uptime-industries/compute-blade/docs/docs/blade/compatibility/switch.md

# Network Switches & PoE Injectors

PoE enabled switch & Injectors which have been used with the Compute Blade

## Cisco
| Product | Model Number | Tested By |
| :--- | :--- | --- |
| Cisco Catalyst 3650 48-FQM | [WS-C3650-48FQM](https://www.cisco.com/c/en/us/products/collateral/switches/catalyst-3650-series-switches/data_sheet-c78-729449.html) | murraythegoz(On Discord) |

## Ubiquiti

| Product | Model Number | Tested By |
| :--- |:--- | --- |
| 8 PoE (Gen1) | [US-8-60W](https://techspecs.ui.com/unifi/switching/us-8-60w) | [einsteinagogo](https://github.com/einsteinagogo) |
| Ultra 60W | [USW-Ultra-60W](https://store.ui.com/us/en/products/usw-ultra-60w) | [dstewart1673](https://github.com/dstewart1673) |
| USW Lite 8 PoE | [USW-LITE-8-POE](https://store.ui.com/us/en/products/usw-lite-8-poe) | [khrystoph](https://github.com/khrystoph) |
| Standard 24 PoE (Gen1) | [US-24-250W](https://techspecs.ui.com/unifi/switching/us-24-250w) | [einsteinagogo](https://github.com/einsteinagogo) |
| Pro 24 PoE | [USW-Pro-24-PoE](https://techspecs.ui.com/unifi/switching/usw-pro-24-poe) | [Uptime](https://github.com/uptime-lab) |
| Pro 48 PoE | [USW-Pro-48-PoE](https://techspecs.ui.com/unifi/switching/usw-pro-48-poe) | [adriano](https://github.com/Adriano8899) |
| PoE+ Adapter (30W) | [U-POE-at](https://techspecs.ui.com/unifi/accessories/u-poe-at) | [mindspore](https://github.com/cKhoff) |
| Pro Max 24 PoE | [USW-Pro-Max-24-PoE](https://techspecs.ui.com/unifi/switching/usw-pro-max-24-poe) | [mindspore](https://github.com/cKhoff) |
| USW Enterprise 8 PoE | [USW-Enterprise-8-PoE (120W)](https://store.ui.com/us/en/category/switching-utility/products/usw-enterprise-8-poe) | [Tom](https://github.com/nyx0) |

## TP-Link

| Product | Model Number | Tested By |
| :--- | :--- | --- |
| TL-SG105MPE | [TL-SG105MPE](https://www.tp-link.com/us/home-networking/5-port-switch/tl-sg105mpe/) | slipstickn(On Discord) |

## Juniper

| Product | Model Number | Tested By |
| :--- |:--- | --- |
| EX2200-48P-4G | [EX2200-48P-4G](https://www.juniper.net/documentation/product/us/en/ex2200/) | [mookie-](https://github.com/mookie-) |

## Brocade

| Product | Model Number | Tested By |
| :--- |:--- | --- |
| ICX 6610 | [ICX 6610-48P](https://webresources.ruckuswireless.com/pdf/datasheets/ds-icx-6610.pdf) | [khrystoph](https://github.com/khrystoph) |

## Mikrotik

| Product | Model Number | Tested By |
| :--- |:--- | --- |
| CRS328-24P-4S+RM | [CRS328-24P-4S+RM](https://mikrotik.com/product/crs328_24p_4s_rm) | [Metrotyranno](https://github.com/metrotyranno) |
| CRS354-48P-4S+2Q+RM | [CRS354-48P-4S+2Q+RM](https://mikrotik.com/product/crs354_48p_4s_2q_rm) | [Metrotyranno](https://github.com/metrotyranno) |
