uptime-industries/compute-blade/docs/docs/bladerunner/19inch/index.mdx

---
sidebar_position: 2
---

# 19 inch Rack

BladeRunner™️ 19-Inch

The Enterprise 19-Inch Enclosure is for deployment at scale. Can be equipped with twenty Compute Blades and ten Fan Units, offering high density compute in a standard 1U of rack space.

Download the [Datasheet](/datasheet/BladeRunner_datasheet_v.1.0.pdf) (PDF)

## Drawing
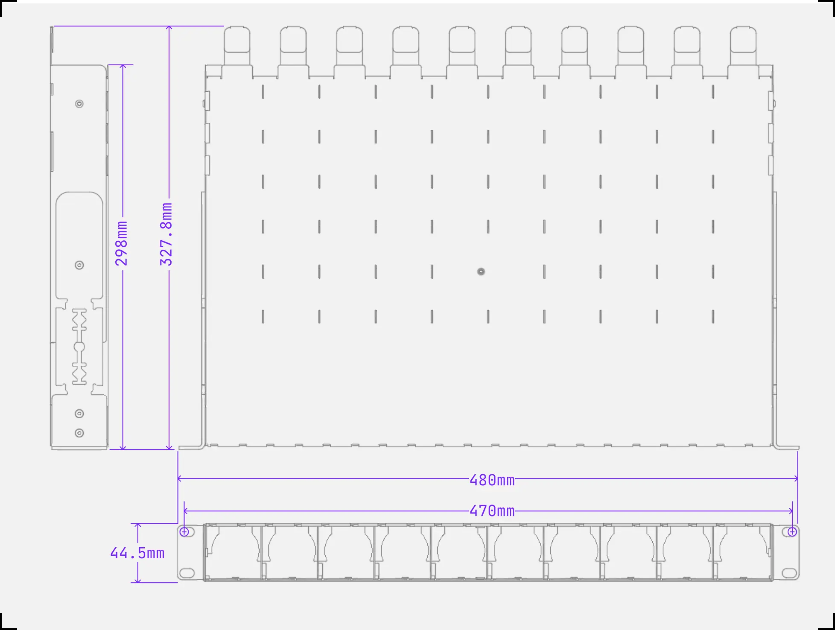
[picture p19: docs/static/img/bladerunner/19/19-drawing.webp]
Drawing with dimensions


## 3D Files

Files for the BladeRunners™️ 19 Inch are available on [GitHub](https://github.com/uptime-lab/compute-blade/tree/main/bladerunner/quad)
