uptime-industries/compute-blade/docs/docs/bladerunner/2node/index.mdx

---
sidebar_position: 3
---

# 2-node

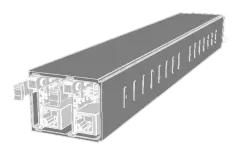
[picture p20: docs/static/img/bladerunner/twin/bladerunner-twin.webp]
BladeRunner™️ 2-Node


2-Node Enclosure allows two Compute Blades and one Fan Unit to be installed. It is ideal for desktop and development.

Download the [Datasheet](/datasheet/BladeRunner_datasheet_v.1.0.pdf) (PDF)

## Drawing
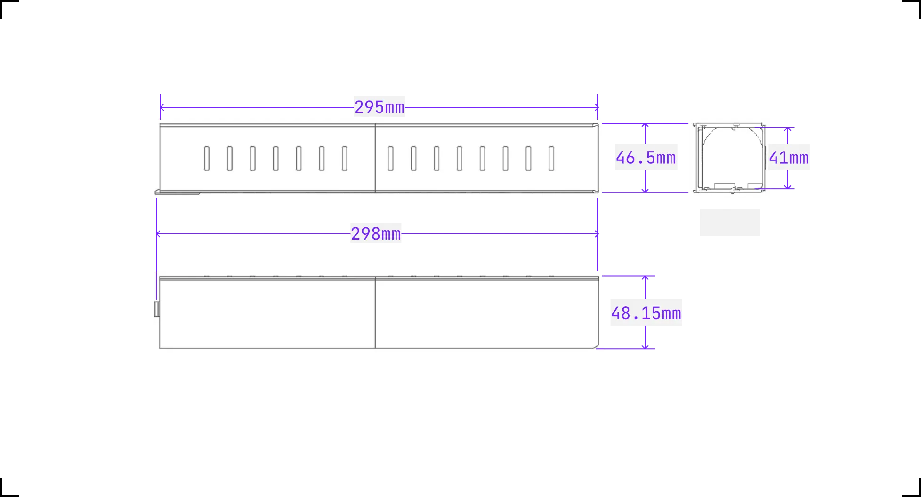
[picture p21: docs/static/img/bladerunner/twin/twin-drawing.webp]
Drawing with dimensions


## 3D Files

Files for the BladeRunners™️ 2-Node are available on [GitHub](https://github.com/uptime-lab/compute-blade/tree/main/models/bladerunner/twin)
