uptime-industries/compute-blade/docs/docs/bladerunner/4node/index.mdx

---
sidebar_position: 2
---

# 4-node

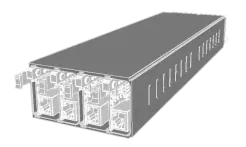
[picture p22: docs/static/img/bladerunner/quad/bladerunner-quad.webp]
BladeRunner™️ 4-node


The 4-node BladeRunner™️ is our recommend enclosure for Homelab and cluster development.
Capable of holding four Compute Blades and two Fan Units, it is ideal for quickly spinning up a development environment.

Download the [Datasheet](/datasheet/BladeRunner_datasheet_v.1.0.pdf) (PDF)

## Drawing

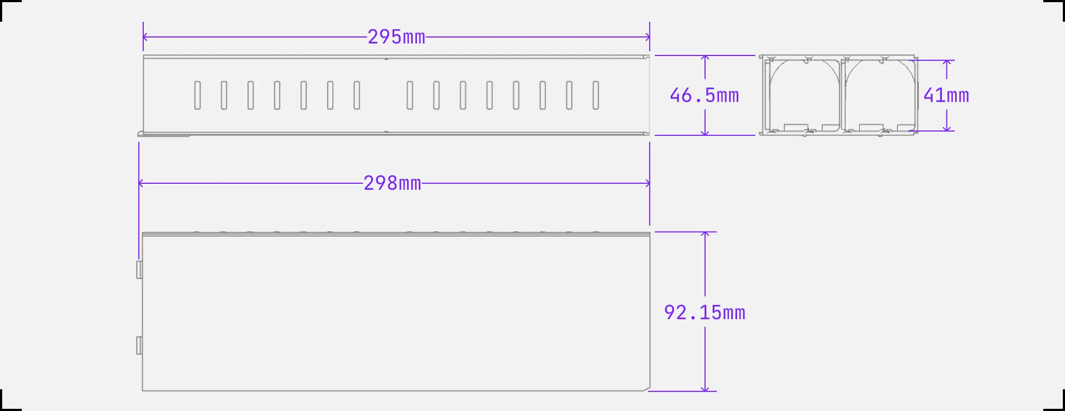
[picture p23: docs/static/img/bladerunner/quad/quad-drawing.webp]
Drawing with dimensions


## 3D Files

Files for the 4-node BladeRunners™️ are available on [GitHub](https://github.com/uptime-lab/compute-blade/tree/main/bladerunner/quad)
