uptime-industries/compute-blade/docs/docs/bladerunner/twin/index.mdx

---
sidebar_position: 2
---

# 2-node

BladeRunner™️ 2-Node

2-Node Enclosure allows two Compute Blades and one Fan Unit to be installed. It is ideal for desktop and development.

## Drawing
Drawing with dimensions

## 3D Files

Files for the BladeRunners™️ 2-Node are available on [GitHub](https://github.com/uptime-industries/compute-blade/tree/main/bladerunner/twin)
