uptime-industries/compute-blade/fan-unit/img/5x_Fan_Units.jpg

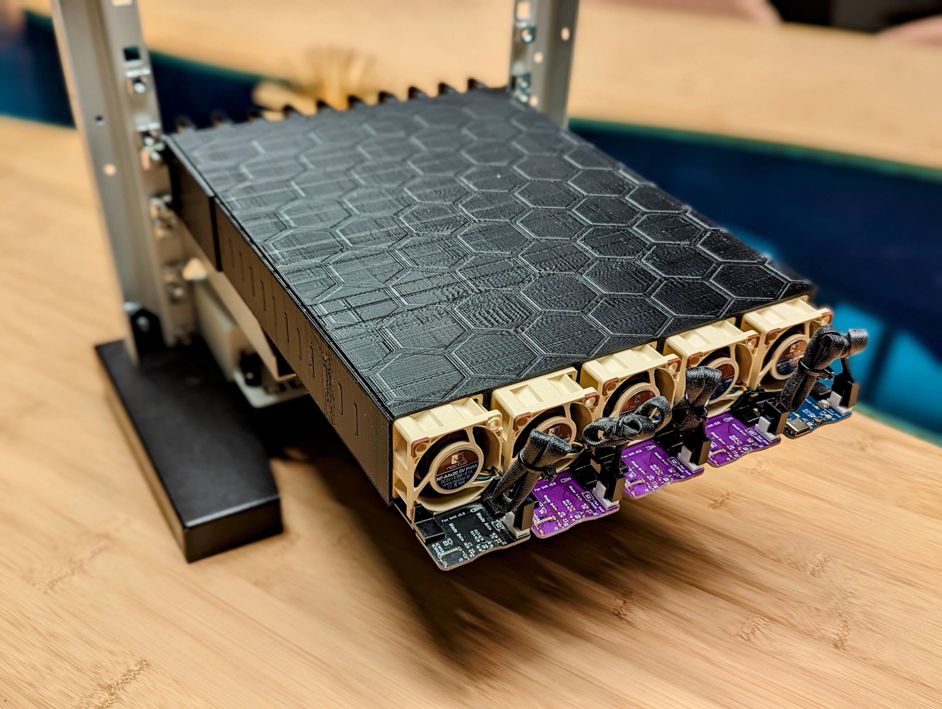
fan-unit/img/5x_Fan_Units.jpg
