uptime-industries/compute-blade/fan-unit/img/Fan_Unit_v0.6.jpg

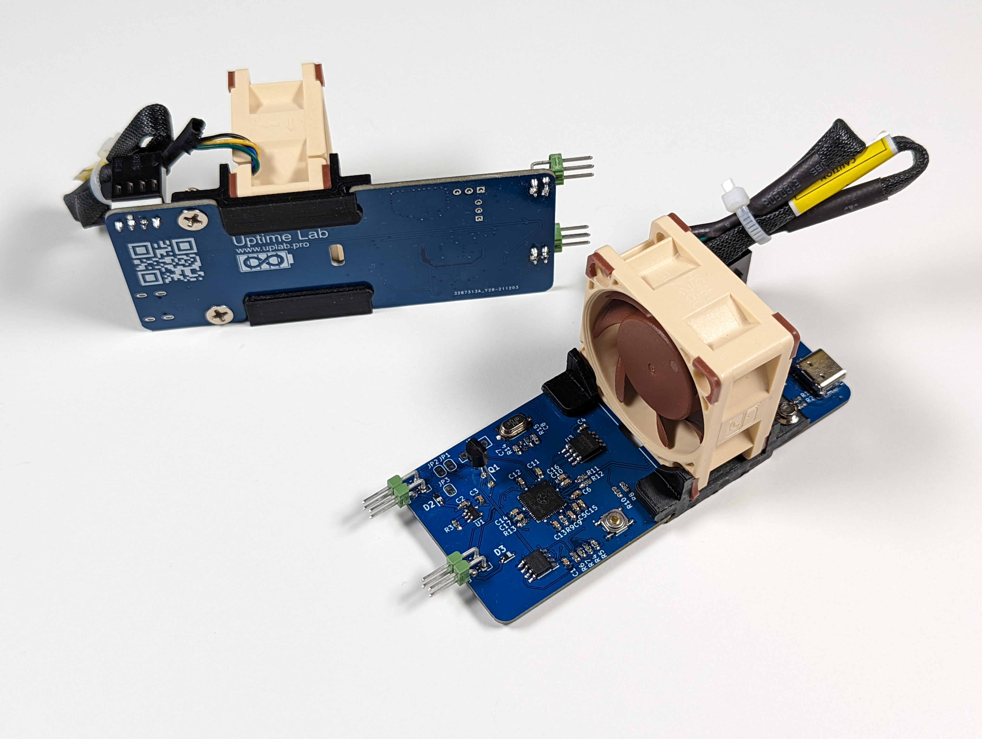
fan-unit/img/Fan_Unit_v0.6.jpg
