uptime-industries/compute-blade/fan-unit/img/Fan_Unit_v0.8.jpg

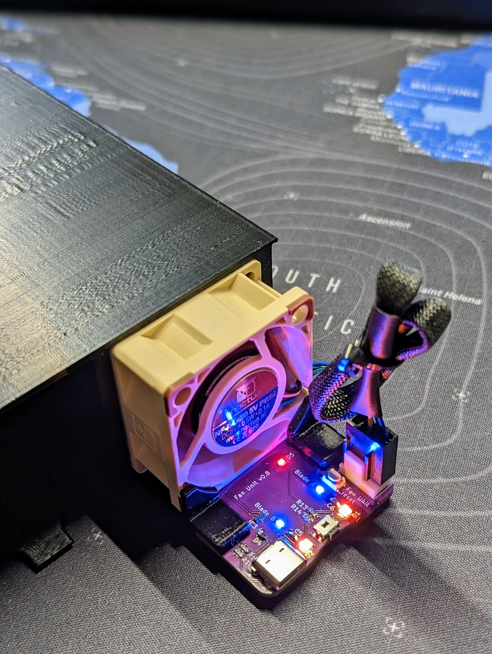
fan-unit/img/Fan_Unit_v0.8.jpg
