uptime-industries/compute-blade/fan-unit/img/Fan_Unit_v0.8_1.jpg

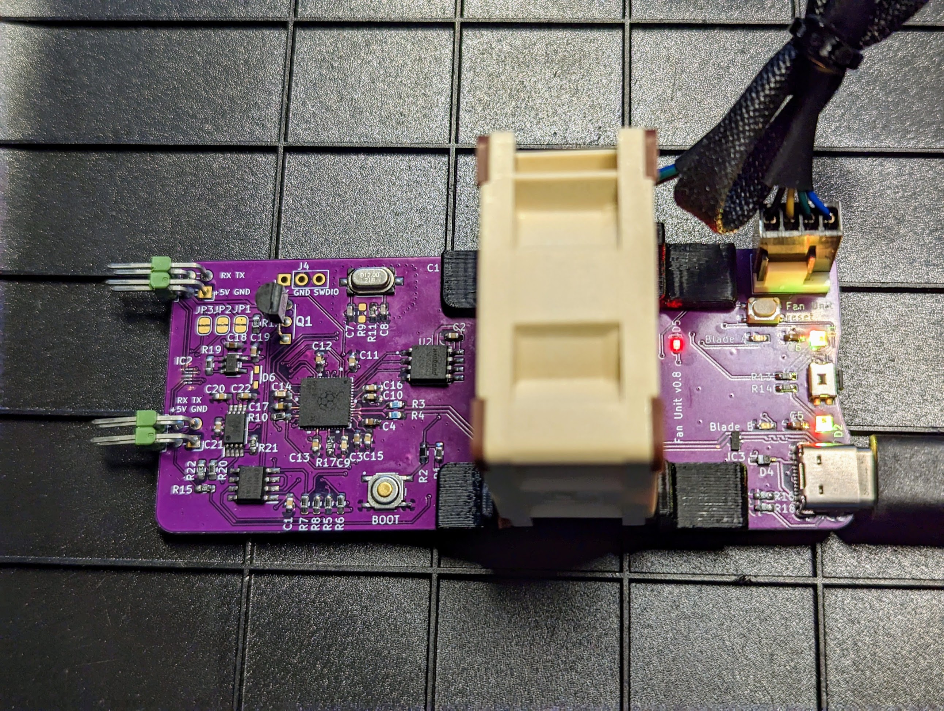
fan-unit/img/Fan_Unit_v0.8_1.jpg
