uptime-industries/compute-blade/fan-unit/fan-bracket/right.stl

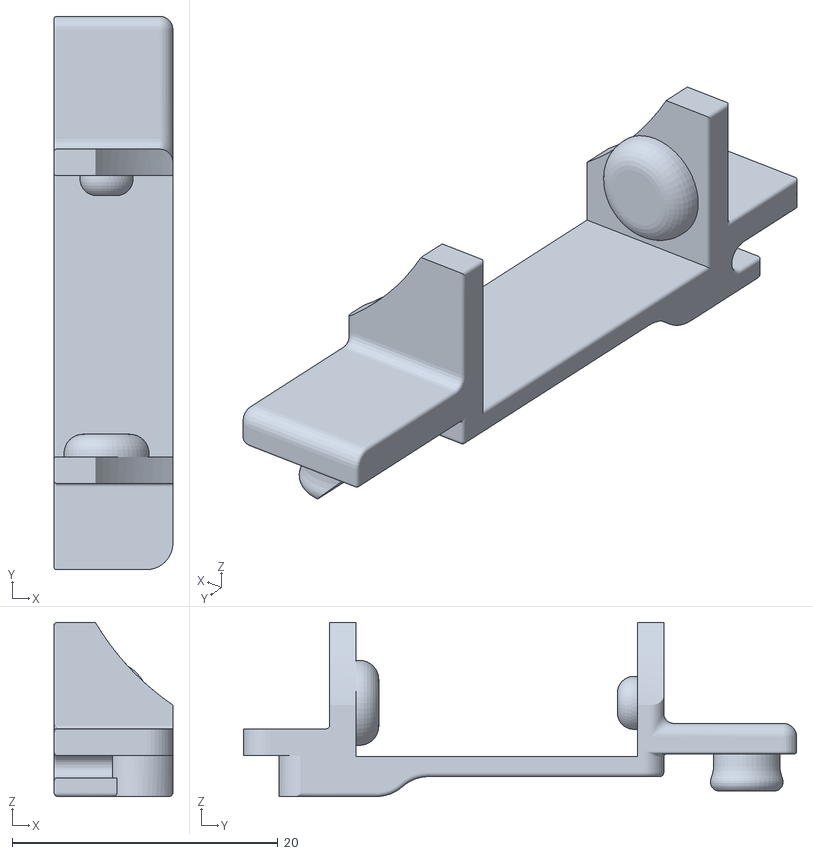
[picture p79: CAD file, 2024-06-19, an earlier design]
fan-unit/fan-bracket/right.stl
8.95 x 41.7 x 13.1
